pc0808f/Taiwanduino/hardware/pic/solder-mask-bottom.png

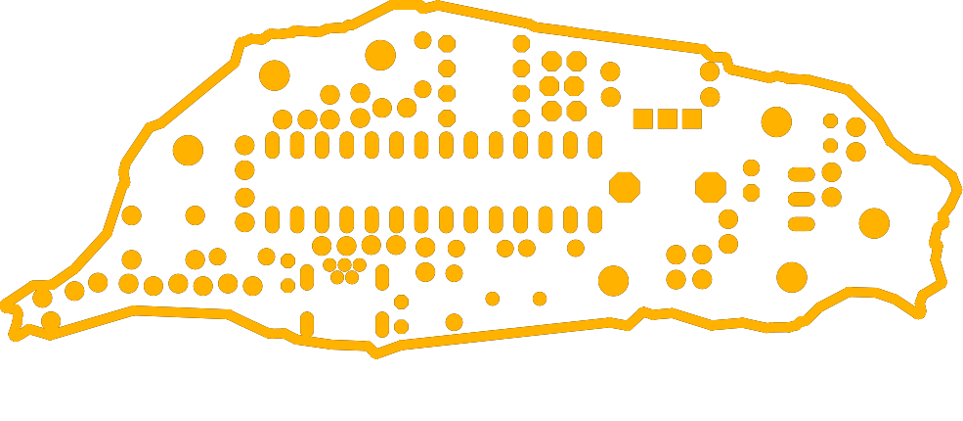
hardware/pic/solder-mask-bottom.png
