pc0808f/Taiwanduino/hardware/pic/solder-mask-top.png

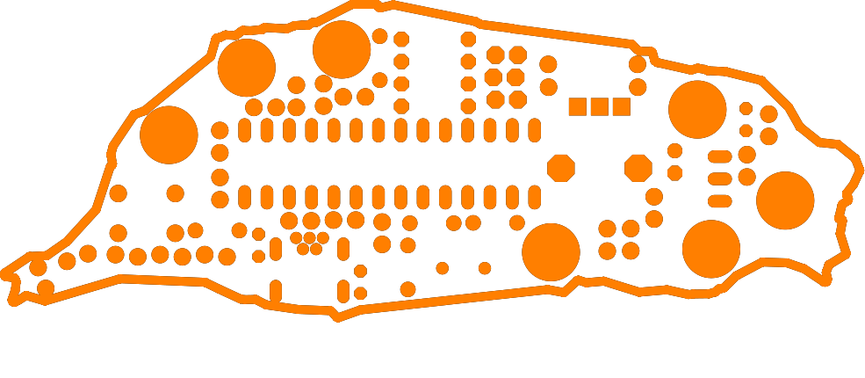
hardware/pic/solder-mask-top.png
